jescarri/lora-node/power-profile/runtime_after_gpio_hold.png

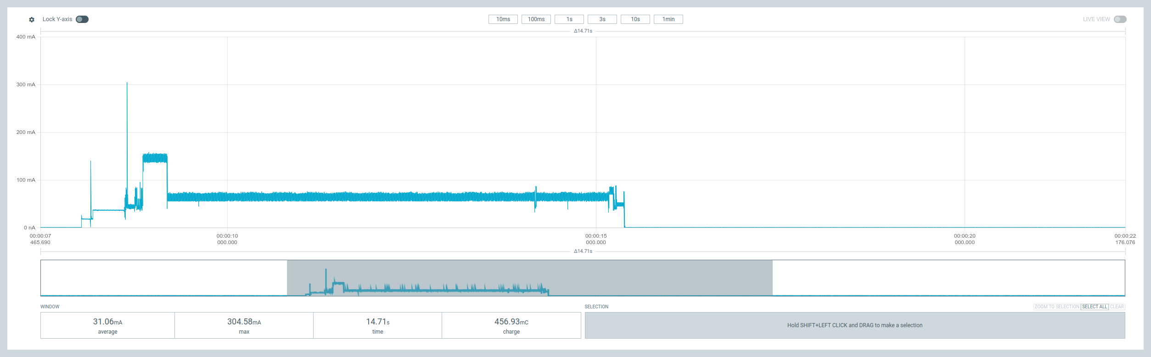
power-profile/runtime_after_gpio_hold.png
