jescarri/lora-node/power-profile/runtime_before_gpio_hold.png

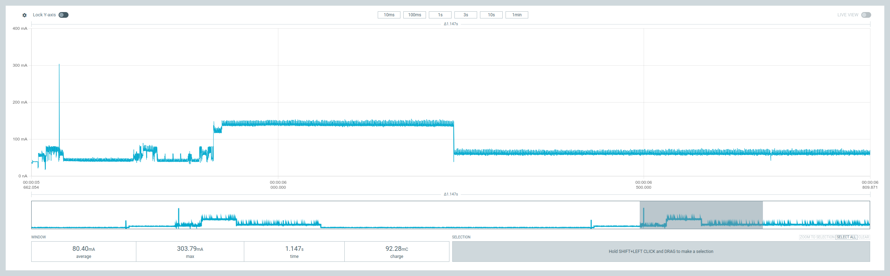
power-profile/runtime_before_gpio_hold.png
