jescarri/lora-node/power-profile/sleep_after_gpio_hold.png

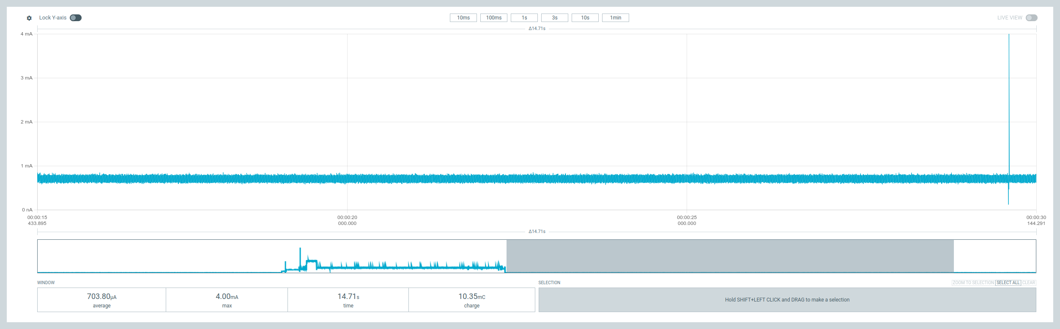
power-profile/sleep_after_gpio_hold.png
