jescarri/lora-node/power-profile/sleep_before_gpio_hold.png

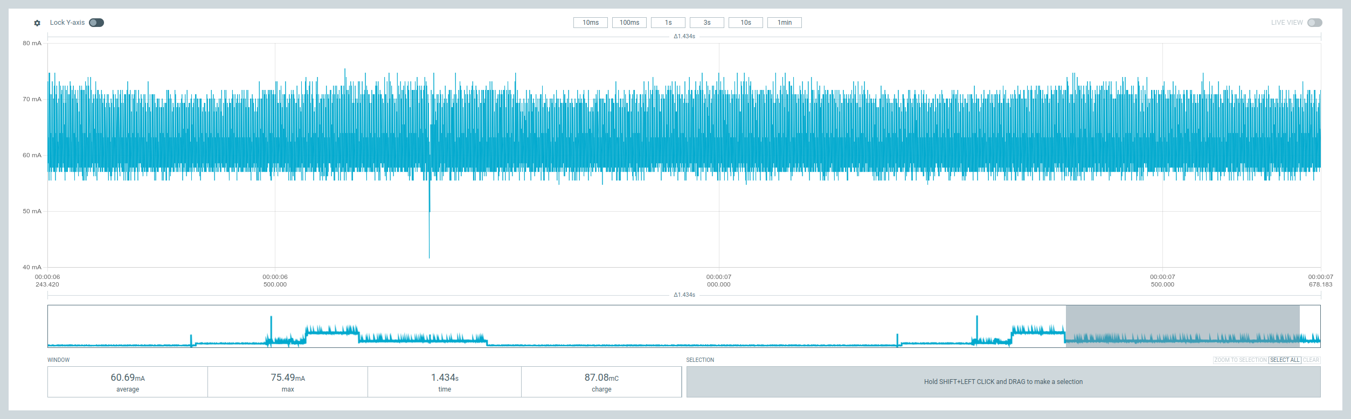
power-profile/sleep_before_gpio_hold.png
