jescarri/lora-node/power-profile/v1.0.0/active_transmission.png

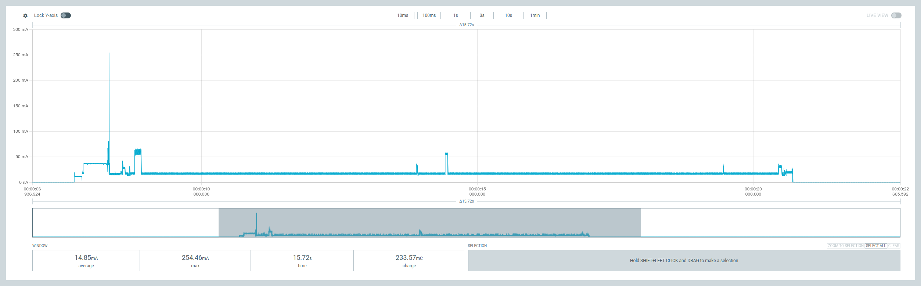
power-profile/v1.0.0/active_transmission.png
