jescarri/lora-node/power-profile/v1.0.0/sleep_time.png

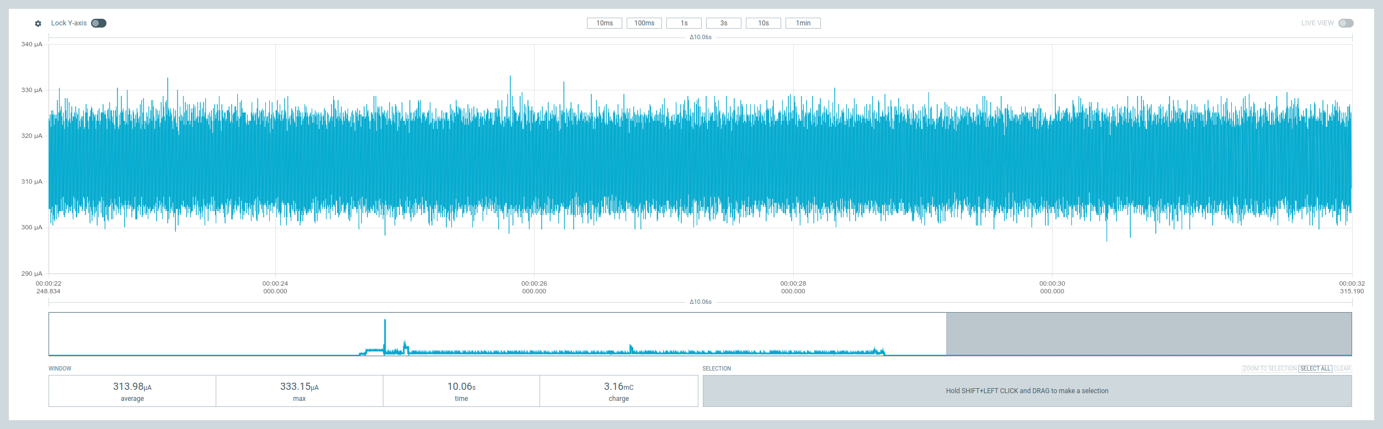
power-profile/v1.0.0/sleep_time.png
